felhub/diy_mm/simulation/DIY Mic Electronics Sim.asc

C1: polcap; 33µ; V=25 Irms=160m Rser=0.89 Lser=1.82791n mfg="Würth Elektronik" pn="865080442006 WCAP-ASLI 5x5,5" type="Al electrolytic"
C2: polcap; 33µ; V=25 Irms=160m Rser=0.89 Lser=1.82791n mfg="Würth Elektronik" pn="865080442006 WCAP-ASLI 5x5,5" type="Al electrolytic"
C3: polcap; 33µ; V=25 Irms=160m Rser=0.89 Lser=1.82791n mfg="Würth Elektronik" pn="865080442006 WCAP-ASLI 5x5,5" type="Al electrolytic"
C4: cap; 100n
C5: polcap; 33µ; V=25 Irms=160m Rser=0.89 Lser=1.82791n mfg="Würth Elektronik" pn="865080442006 WCAP-ASLI 5x5,5" type="Al electrolytic"
C6: cap; 1n
C7: polcap; 33µ; V=25 Irms=160m Rser=0.89 Lser=1.82791n mfg="Würth Elektronik" pn="865080442006 WCAP-ASLI 5x5,5" type="Al electrolytic"
C8: cap; 1µ
C9: cap; 47µ
C10: cap; 47µ
Q1: npn; BC849C
Q2: pnp; BC859C
Q3: npn; BC849C
Q4: npn; BC849C
R1: res; 33k
R2: res; 33k
R3: res; 10k
R4: res; 33k
R5: res; 220
R6: res; 2.2k
R7: res; 2.2k
R8: res; 100
R9: res; 100
R10: res; 100k
R11: res; 100k
R12: res; 6.8k
R13: res; 6.8k
R14: res; 100k
R15: res; 33k
R16: res; 100k
U1: BZT52C10
V1: voltage; 48
V2: voltage; SINE(0 0.5 AC 1.)
Named nets: 0, 10V, IN, OUThot, OUTcold
.SUBCKT BC849C 1 2 3 
Q1 1 2 3 Transistor 0.9342
Q2 11 2 3 Transistor 0.0658
RQ 1 11 662.1
D1 2 1 Diode
*
.MODEL Transistor NPN
+ IS = 1.641E-014
+ NF = 0.9969
+ ISE = 1.151E-016
+ NE = 1.208
+ BF = 509
+ IKF = 0.0863
+ VAF = 66.64
+ NR = 0.9953
+ ISC = 1.068E-014
+ NC = 1.357
+ BR = 9.832
+ IKR = 0.1524
+ VAR = 25
+ RB = 360
+ IRB = 2.5E-005
+ RBM = 0.8
+ RE = 0.6403
+ RC = 0.5461
+ XTB = 1.595
+ EG = 1.11
+ XTI = 6.27
+ CJE = 1.119E-011
+ VJE = 0.6755
+ MJE = 0.3391
+ TF = 5.25E-010
+ XTF = 22.74
+ VTF = 2
+ ITF = 0.368
+ PTF = 0
+ CJC = 3.693E-012
+ VJC = 0.5083
+ MJC = 0.3642
+ XCJC = 1
+ TR = 0.0008
+ CJS = 0
+ VJS = 0.75
+ MJS = 0.333
+ FC = 0.9552
.MODEL Diode D
+ IS = 4.418E-016
+ N = 0.9799
+ BV = 1000
+ IBV = 0.001
+ RS = 3460
+ CJO = 0
+ VJ = 1
+ M = 0.5
+ FC = 0
+ TT = 0
+ EG = 1.11
+ XTI = 3
.ENDS
.SUBCKT BC859B 1 2 3
Q1 1 2 3 MAIN 0.9607
Q2 11 2 3 MAIN 0.03929
RQ 1 11 561.1
D1 1 2 DIODE
*
.MODEL MAIN PNP
+ IS = 1.95E-014
+ NF = 1.022
+ ISE = 1.253E-014
+ NE = 1.577
+ BF = 297.2
+ IKF = 0.0831
+ VAF = 41.13
+ NR = 1.021
+ ISC = 1.791E-016
+ NC = 1.183
+ BR = 10.02
+ IKR = 0.02503
+ VAR = 16.61
+ RB = 220
+ IRB = 2.5E-005
+ RBM = 0.9
+ RE = 1.045
+ RC = 0.2657
+ XTB = 1.28
+ EG = 1.11
+ XTI = 2.944
+ CJE = 1.095E-011
+ VJE = 0.6608
+ MJE = 0.375
+ TF = 1.2E-009
+ XTF = 3
+ VTF = 3.813
+ ITF = 0.1208
+ PTF = 0
+ CJC = 5.88E-012
+ VJC = 0.5428
+ MJC = 0.39
+ XCJC = 0.459
+ TR = 8.8E-008
+ CJS = 0
+ VJS = 0.75
+ MJS = 0.333
+ FC = 0.9501
.MODEL DIODE D
+ IS = 7.703E-015
+ N = 1.146
+ BV = 1000
+ IBV = 0.001
+ RS = 2.826E+004
+ CJO = 0
+ VJ = 1
+ M = 0.5
+ FC = 0
+ TT = 0
+ EG = 1.11
+ XTI = 3
.ENDS
.ac dec 10 20 20000
.subckt 865080442006_33uF 1 2
Rser 1 3 0.89
Lser 2 4 1.827910305E-09
C 3 4 0.000033
Rpar 3 4 3030303.03030303
.ends 865080442006_33uF
